SUWS/morse-practice-oscillator/Mechanicial/Key/textures/key_key_r1.0_inner.png

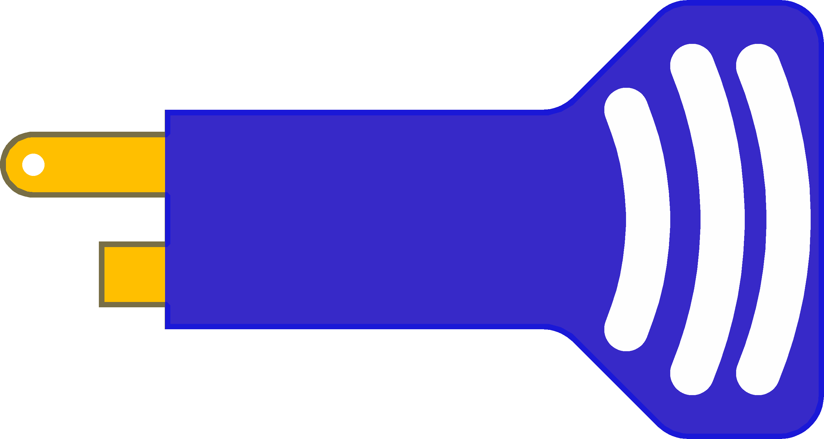
Mechanicial/Key/textures/key_key_r1.0_inner.png
