SUWS/morse-practice-oscillator/Mechanicial/Sounder/textures/sounder_PCB_r2.0_bottom.png

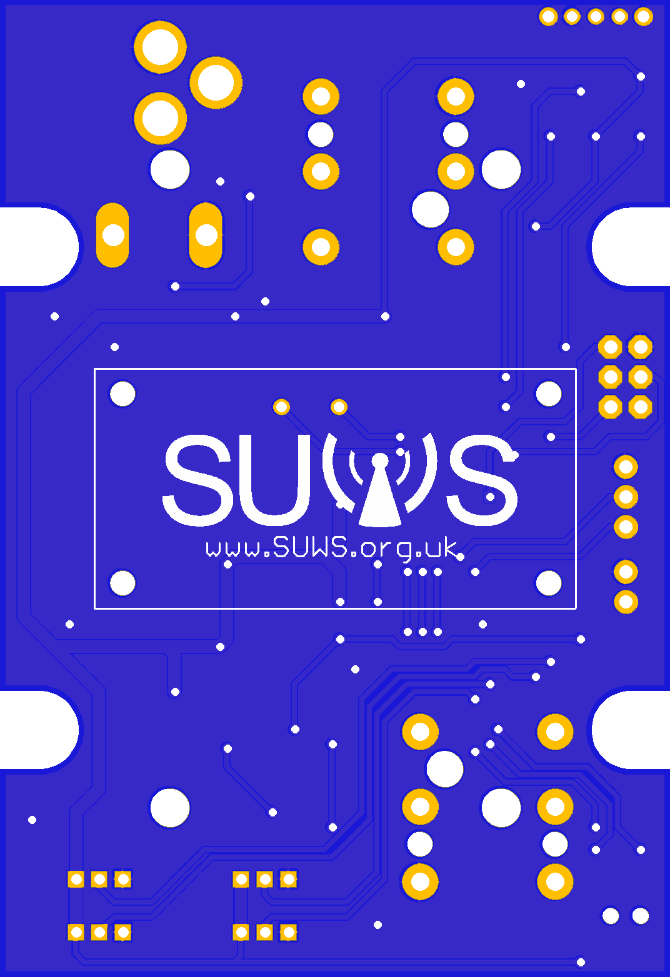
Mechanicial/Sounder/textures/sounder_PCB_r2.0_bottom.png
