SUWS/morse-practice-oscillator/Mechanicial/Sounder/textures/sounder_rear_jack_panel_r2.0_rear.png

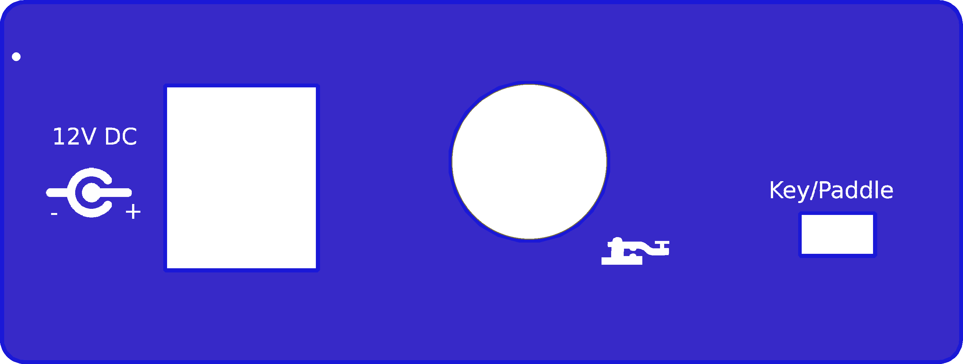
Mechanicial/Sounder/textures/sounder_rear_jack_panel_r2.0_rear.png
