SUWS/morse-practice-oscillator/LTSpice/ClicklessOscilator.asc

C1: cap; 10nF
C2: cap; 100µF
C3: cap; 20nF
C4: cap; 10nF
C5: cap; 10nF
C6: cap; 100µF
C7: cap; 100µF
C8: cap; 100µF
C9: cap; 20nF
C10: cap; 10nF
C11: cap; 10nF
C12: cap; 100nF
C13: cap; 100µF
C14: cap; 200nF
Q1: npn; 2N3904
Q2: npn; 2N3904
Q3: npn; 2N3904
R1: res; 100K
R2: res; 100K
R3: res; 47K
R4: res; 10K
R5: res; 10K
R6: res; 33K
R7: res; 33K
R8: res; 1K
R9: res; 10
R10: res; 10K
R11: res; 10K
R12: res; 22K
R13: res; 22K
R14: res; 22K
R15: res; 220K
R16: res; 220K
R17: res; 10K
R18: res; 330
R19: res; 330
R20: res; 10K
R21: res; 10K
R22: res; 10K
R23: res; 3K
R24: res; 7K
R25: res; 15K
R26: res; 1K
R27: res; 8
U1: opamp2; LM324
U2: opamp2; LM324
U3: opamp2; LM324
U4: opamp2; LM324
V1: voltage; 12V
V2: voltage; PULSE(0 12 1 0 0 1 2)
Named nets: 0, +Vf, TriangleOutput, SineOutput, +V, +V/2, KeyerInput12v, VCAOut, Spkr
.tran 10s
.lib LM324.sub
.lib LM386.sub
