SUWS/morse-practice-oscillator/LTSpice/ClicklessOscilator_WithToneControl.asc

C6: cap; 100µF
C7: cap; 100µF
C8: cap; 100µF
C9: cap; 20nF
C10: cap; 10nF
C11: cap; 10nF
C12: cap; 0.047µF
C13: cap; 0.047µF
C14: cap; 0.018µF
C15: cap; 0.018µF
Q1: npn; 2N3904
Q2: npn; 2N3904
Q3: npn; 2N3904
Q4: npn; MPSA42
R8: res; 1K
R9: res; 10
R10: res; 10K
R11: res; 10K
R12: res; 22K
R13: res; 22K
R14: res; 22K
R15: res; 220K
R16: res; 220K
R17: res; 10K
R18: res; 330
R19: res; 330
R20: res; 10K
R21: res; 10K
R22: res; 10K
R23: res; 18K
R24: res; 18K
R25: res; 4K7
R26: res; 7K
U4: opamp2; LM324
V1: voltage; 12V
V2: voltage; PULSE(0 12 1 0 0 1 2)
Named nets: +Vf, 0, +V, +V/2, KeyerInput12v, SineOutput, VCAOut, sineoutput
.tran 10s startup
.lib LM324.sub
.lib MPSA42.lib
