SUWS/morse-practice-oscillator/firmware/wave.c

/********************************************************************
 File Description:

 Contains a pregenerated sine wave

********************************************************************/

#include "wave.h"
#include <avr/pgmspace.h>

uint16_t PROGMEM const sintab2[512] =
{
	2048, 2073, 2098, 2123, 2148, 2174, 2199, 2224,
	2249, 2274, 2299, 2324, 2349, 2373, 2398, 2423,
	2448, 2472, 2497, 2521, 2546, 2570, 2594, 2618,
	2643, 2667, 2690, 2714, 2738, 2762, 2785, 2808,
	2832, 2855, 2878, 2901, 2924, 2946, 2969, 2991,
	3013, 3036, 3057, 3079, 3101, 3122, 3144, 3165,
	3186, 3207, 3227, 3248, 3268, 3288, 3308, 3328,
	3347, 3367, 3386, 3405, 3423, 3442, 3460, 3478,
	3496, 3514, 3531, 3548, 3565, 3582, 3599, 3615,
	3631, 3647, 3663, 3678, 3693, 3708, 3722, 3737,
	3751, 3765, 3778, 3792, 3805, 3817, 3830, 3842,
	3854, 3866, 3877, 3888, 3899, 3910, 3920, 3930,
	3940, 3950, 3959, 3968, 3976, 3985, 3993, 4000,
	4008, 4015, 4022, 4028, 4035, 4041, 4046, 4052,
	4057, 4061, 4066, 4070, 4074, 4077, 4081, 4084,
	4086, 4088, 4090, 4092, 4094, 4095, 4095, 4095,
	4095, 4095, 4095, 4095, 4094, 4092, 4090, 4088,
	4086, 4084, 4081, 4077, 4074, 4070, 4066, 4061,
	4057, 4052, 4046, 4041, 4035, 4028, 4022, 4015,
	4008, 4000, 3993, 3985, 3976, 3968, 3959, 3950,
	3940, 3930, 3920, 3910, 3899, 3888, 3877, 3866,
	3854, 3842, 3830, 3817, 3805, 3792, 3778, 3765,
	3751, 3737, 3722, 3708, 3693, 3678, 3663, 3647,
	3631, 3615, 3599, 3582, 3565, 3548, 3531, 3514,
	3496, 3478, 3460, 3442, 3423, 3405, 3386, 3367,
	3347, 3328, 3308, 3288, 3268, 3248, 3227, 3207,
	3186, 3165, 3144, 3122, 3101, 3079, 3057, 3036,
	3013, 2991, 2969, 2946, 2924, 2901, 2878, 2855,
	2832, 2808, 2785, 2762, 2738, 2714, 2690, 2667,
	2643, 2618, 2594, 2570, 2546, 2521, 2497, 2472,
	2448, 2423, 2398, 2373, 2349, 2324, 2299, 2274,
	2249, 2224, 2199, 2174, 2148, 2123, 2098, 2073,
	2048, 2023, 1998, 1973, 1948, 1922, 1897, 1872,
	1847, 1822, 1797, 1772, 1747, 1723, 1698, 1673,
	1648, 1624, 1599, 1575, 1550, 1526, 1502, 1478,
	1453, 1429, 1406, 1382, 1358, 1334, 1311, 1288,
	1264, 1241, 1218, 1195, 1172, 1150, 1127, 1105,
	1083, 1060, 1039, 1017,  995,  974,  952,  931,
	910,  889,  869,  848,  828,  808,  788,  768,
	749,  729,  710,  691,  673,  654,  636,  618,
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
};

uint16_t WaveGetPoint(uint16_t pos)
{
    return pgm_read_word_near(sintab2 + pos);
}
