SUWS/morse-practice-oscillator/firmware/wave.h

/********************************************************************
 File Description:

 definitions for the I2C interface

********************************************************************/

#include <stdint.h>

#ifndef WAVE_H_
#define WAVE_H_

/* FUNCTION DECLARATIONS *******************************************/

uint16_t WaveGetPoint(uint16_t pos);

#endif /* WAVE_H_ */
