SUWS/morse-practice-oscillator/firmware/uart.h

/********************************************************************
 File Description:

 definitions for the debug uart interface

********************************************************************/

#ifndef UART_H_
#define UART_H_

/* FUNCTION DECLARATIONS *******************************************/

void UartInit();
int UartPutString(char* str);

#endif /* UART_H_ */
